dnkorte/log_temp_humid/config.py

# This file is where you keep basic configuration info of the non-super-secret flavor

config = {
    'feed_T' : 'temperature-office',
    'feed_H' : 'humidity-office',
    'feed_T_outdoor' : 'temperature-outdoor',
    'feed_H_outdoor' : 'humidity-outdoor',
    'weather_location' : 'Flint, US'
    }
